DrJonEA/RPIPicoW-RelayControl/src/MQTTRouterRelay.cpp

/*
 * MQTTRouterRelay.cpp
 *
 *  Created on: 4 Oct 2022
 *      Author: jondurrant
 */

#include "MQTTRouterRelay.h"
#include "MQTTTopicHelper.h"

#define Relay_TOPIC  "Relay"
#define PAYLOAD_ON "on"

MQTTRouterRelay::MQTTRouterRelay(RelayAgent *agent) {
	pAgent = agent;
}

MQTTRouterRelay::~MQTTRouterRelay() {
	// Nop
}



/***
 * Use the interface to setup all the subscriptions
 * @param interface
 */
void MQTTRouterRelay::subscribe(MQTTInterface *interface){
	MQTTRouterTwin::subscribe(interface);
	//Init topic if needed
	if (pLedTopic == NULL){
		const char *id = interface->getId();
		pLedTopic = (char *)pvPortMalloc(
			MQTTTopicHelper::lenThingTopic(id, MQTT_Relay_REQ_TOPIC)
			);
		if (pLedTopic != NULL){
			MQTTTopicHelper::genThingTopic(pLedTopic, id, MQTT_Relay_REQ_TOPIC);
		} else {
			LogError( ("Unable to allocate topic") );
		}
	}
	if (pLedTopic != NULL){
		interface->subToTopic(pLedTopic, 1);
	}
}

/***
 * Route the message the appropriate part of the application
 * @param topic
 * @param topicLen
 * @param payload
 * @param payloadLen
 * @param interface
 */
void MQTTRouterRelay::route(const char *topic,
		size_t topicLen,
		const void * payload,
		size_t payloadLen,
		MQTTInterface *interface){

	MQTTRouterTwin::route(topic, topicLen, payload, payloadLen, interface);

	if (strlen(pLedTopic) == topicLen){
		if (memcmp(topic, pLedTopic, topicLen)==0){
			if (pAgent != NULL){
				pAgent->addJSON(payload, payloadLen);
			}
		}
	}
}
